elcano/Drive-by-wire/Electronics/H_BRIDGE_MOSFET_CIRCUIT_ANALYSIS_V2.asc

ComparatorOutput1: voltage; 5
ComparatorOutput2: voltage; 5
D1: schottky; SB5H100
D2: schottky; SB5H100
D3: schottky; SB5H100
D4: schottky; SB5H100
M1: nmos; 2N7000
M2: nmos; AOD66406
M3: nmos; AOD66406
M4: nmos; 2N7000
M5: pmos; AOD4185
M6: pmos; AOD4185
R1: res; 1000
R2: res; 10000
R3: res; 10000
R4: res; 1000
R_MOTOR_LOAD: res; 4
V4: voltage; 5
V5: voltage; 5
V_supply: voltage; 12
Named nets: 0, Node_1, Node_Drain
.op
