elcano/Drive-by-wire/Electronics/MOSFET_SWITCH_CIRCUIT_ANALYSIS_LOW_LEVEL_4.1_V3A.asc

12V_Supply: voltage; 5
24V_ACTIVE: LED; NSCW100
24V_Supply: voltage; 10
A1: inv
BRAKE_ON_SIGNAL: voltage; 5
BRAKE_VOLT_SIGNAL: voltage; 0
BRAKES_ON: LED; NSCW100
D1: schottky; MBR745
D2: schottky; MBR745
D3: schottky; MBR20100CT
D4: schottky; MBR20100CT
D5: schottky; MBR745
D6: schottky; MBR745
M1: pmos; IRF7204
M2: pmos; IRF7204
M3: nmos; IRLR2908
M4: nmos; IRLR2908
Q1: npn; 2N3904
Q2: npn; 2N3904
Q3: npn; 2N3904
Q4: npn; 2N3904
R1: res; 1000
R2: res; 1000
R3: res; 10k
R4: res; 1000
R6: res; 150
R7: res; 10k
R8: res; 1000
R9: res; 1k
R10: res; 10k
R11: res; 100
R12: res; 1k
R13: res; 100
R_PULLUP_1: res; 10k
R_PULLUP_2: res; 10k
SOLENOID: res; 6
V1: voltage; 0
V2: voltage; 0
V_2N3904_1: voltage; 5
V_2N3904_2: voltage; 5
Named nets: BRAKE_VOLT, BRAKE_ON, 12V, 24V, 0, SOLENOID_POWER, SOLENOID_COMMON, SOLENOID_OUT
.op
