elcano/Drive-by-wire/Drive_By_Wire/ThrottleController.h

#pragma once
#include "Settings.h"
#include <SPI.h>
#include "PID_v1.h"
#include "DriveMode.h"

class ThrottleController {
private:
  volatile int32_t currentThrottlePWM = 0;
  int throttleSet = 0;
  double speedCyclometerInput_mmPs = 0;
  double PIDThrottleOutput_pwm;
  double desiredSpeed_mmPs = 0;


  PID speedPID;

  static const uint32_t MIN_TICK_TIME_ms = (WHEEL_CIRCUM_MM * 1000) / MAX_SPEED_mmPs;
  static const uint32_t MAX_TICK_TIME_ms = (WHEEL_CIRCUM_MM * 1000) / MIN_SPEED_mmPs;

  static volatile uint32_t tickTime_ms[2];
  uint32_t calcTime_ms[2];
  int32_t prevSpeed_mmPs;

  void write(int32_t address, int32_t value);
  void ThrottlePID(int32_t desiredValue);
  int32_t extrapolateSpeed();
  void computeSpeed();
  void engageThrottle(int32_t input);
  static void tick();
public:

  ThrottleController();
  ~ThrottleController();
  void stop();
  int32_t update(int32_t dSpeed, DriveMode mode);
  int getCurrentThrottlePWM() const;
};
